Sn3akySqu1d/Envirotector/Images/image-8.png

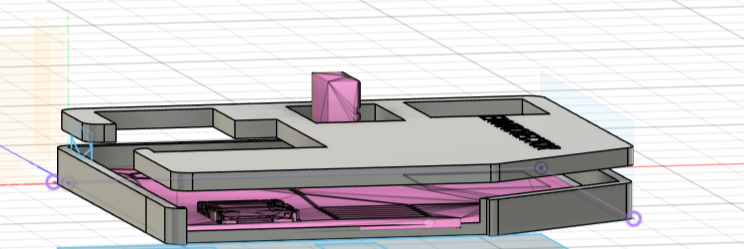
Images/image-8.png
